signalius/MFI_Chip_Rpi_Hat/electronic/RevA/Output/pcb.png

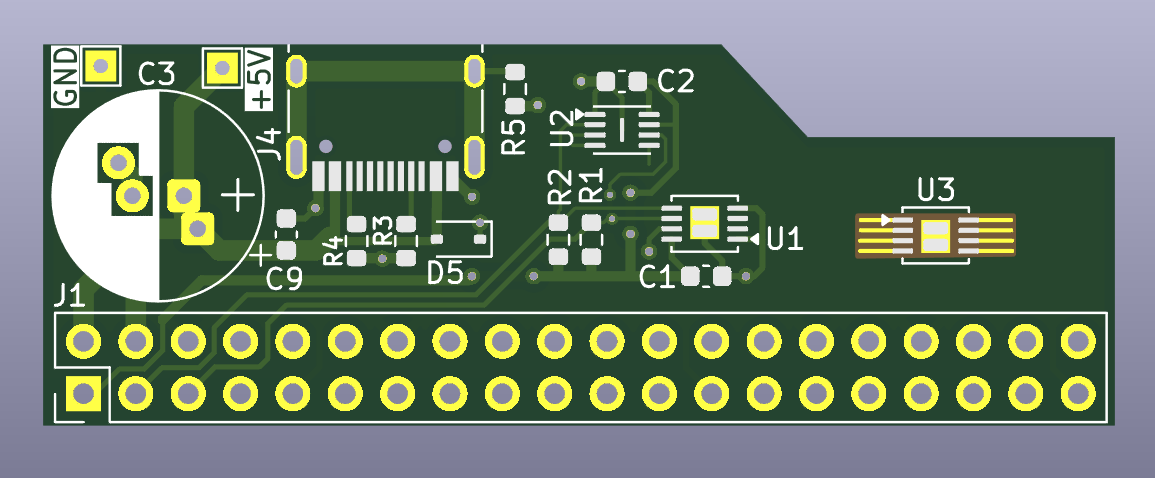
electronic/RevA/Output/pcb.png
